minou65/NMEA2000-FluidLevel/src/favicon.h

// favicon.h

#ifndef _FAVICON_h
#define _FAVICON_h

const uint8_t favicon_ico[] PROGMEM = { // nmea2000-watertank_32x32.png
0x89, 0x50, 0x4E, 0x47, 0x0D, 0x0A, 0x1A, 0x0A, 0x00, 0x00, 0x00, 0x0D, 0x49, 0x48, 0x44, 0x52,
0x00, 0x00, 0x00, 0x20, 0x00, 0x00, 0x00, 0x20, 0x08, 0x02, 0x00, 0x00, 0x00, 0xFC, 0x18, 0xED,
0xA3, 0x00, 0x00, 0x00, 0x09, 0x70, 0x48, 0x59, 0x73, 0x00, 0x00, 0x0B, 0x13, 0x00, 0x00, 0x0B,
0x13, 0x01, 0x00, 0x9A, 0x9C, 0x18, 0x00, 0x00, 0x04, 0x5D, 0x49, 0x44, 0x41, 0x54, 0x48, 0x89,
0xB5, 0x56, 0x5B, 0x48, 0x62, 0x5B, 0x18, 0xFE, 0xB7, 0x24, 0x76, 0x23, 0x4B, 0x6D, 0xA4, 0x54,
0xBA, 0x80, 0xD4, 0x20, 0xF5, 0x10, 0xCD, 0x41, 0x3A, 0x52, 0x69, 0x04, 0x42, 0x0F, 0x0D, 0xC6,
0x64, 0xA8, 0x44, 0x66, 0x78, 0x86, 0x1E, 0xA2, 0xAC, 0xA0, 0x5E, 0x7C, 0x68, 0x1A, 0xE8, 0x18,
0x67, 0x48, 0xF2, 0xC1, 0x1E, 0x4C, 0xBA, 0x42, 0x13, 0x41, 0xD4, 0x43, 0xA7, 0xA2, 0x1B, 0x41,
0x06, 0x41, 0x51, 0x44, 0x90, 0x60, 0xA6, 0xD0, 0x89, 0x4A, 0xCD, 0xCC, 0x48, 0xBB, 0xAD, 0xF3,
0xB0, 0x67, 0x9A, 0x39, 0x93, 0xEE, 0x2E, 0x67, 0xE6, 0x7B, 0xD8, 0x2C, 0xF6, 0xFF, 0xEF, 0xEF,
0x5B, 0xDF, 0x5A, 0xEB, 0x5F, 0xFB, 0xC7, 0x10, 0x42, 0xF0, 0x2B, 0x11, 0x71, 0x3F, 0xF2, 0xFB,
0xFD, 0x17, 0x17, 0x17, 0xDF, 0xC7, 0x10, 0x42, 0x18, 0x86, 0x3D, 0x9F, 0x13, 0xC5, 0xC4, 0xC4,
0xC6, 0xC6, 0xC6, 0xFE, 0x47, 0xA0, 0xBD, 0xBD, 0x7D, 0x66, 0x66, 0x26, 0x31, 0x31, 0xF1, 0xC5,
0x33, 0xFD, 0x1E, 0x2E, 0x97, 0xAB, 0xA8, 0xA8, 0x48, 0xAB, 0xD5, 0x7E, 0x99, 0xA6, 0xC7, 0xE3,
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
0xFB, 0x83, 0xC1, 0xE0, 0xBD, 0x89, 0xCB, 0xCB, 0xCB, 0xC0, 0x65, 0xC0, 0xEB, 0xF5, 0x9E, 0x9C,
0x9C, 0xB8, 0x5C, 0x2E, 0x00, 0xB8, 0xBD, 0xBD, 0xC5, 0x33, 0x43, 0x01, 0x0B, 0x2B, 0xB0, 0xBD,
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
};
#endif
